zNitche/pico-weather-station-v3/pico_weather_station/consts.py

SD_CARD_PATH = "/sd_card"

ADC_VREF = 2.99
ADC_TO_VOLT_CONVERSION_FACTOR = ADC_VREF / 65535

DATA_LOGS_DIR_PATH = f"{SD_CARD_PATH}/data_logs"
LOGS_DIR_PATH = f"{SD_CARD_PATH}/logs"

META_FILE_PATH = f"{SD_CARD_PATH}/meta.txt"
